LokarMotors/AVR-tiny_LoRa/Code/src/config.h

// MSB left
 unsigned char NwkSkey[16] = {0x00, 0x00, 0x00, 0x00, 0x00, 0x00, 0x00, 0x00, 0x00, 0x00, 0x00, 0x00, 0x00, 0x00, 0x00, 0x00};
 unsigned char AppSkey[16] = {0x00, 0x00, 0x00, 0x00, 0x00, 0x00, 0x00, 0x00, 0x00, 0x00, 0x00, 0x00, 0x00, 0x00, 0x00, 0x00};
 unsigned char DevAddr[4] = {0x00, 0x00, 0x00, 0x00};
